kbjunky/MacroPact/src/L0.bmp

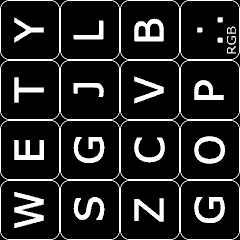
src/L0.bmp
