kbjunky/MacroPact/src/L1.bmp

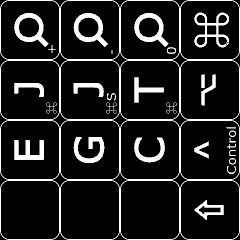
src/L1.bmp
