kbjunky/MacroPact/src/L2.bmp

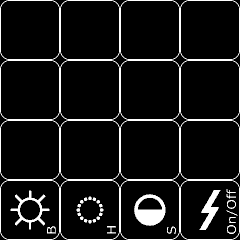
src/L2.bmp
